AnishNagulavancha/Spoil-Free-Fridge/Data logs/pcb_data/house_A_pcb_A_S0001_Anish_control_empty_20260720_190316/images/img_000002_20260720_193534.jpg

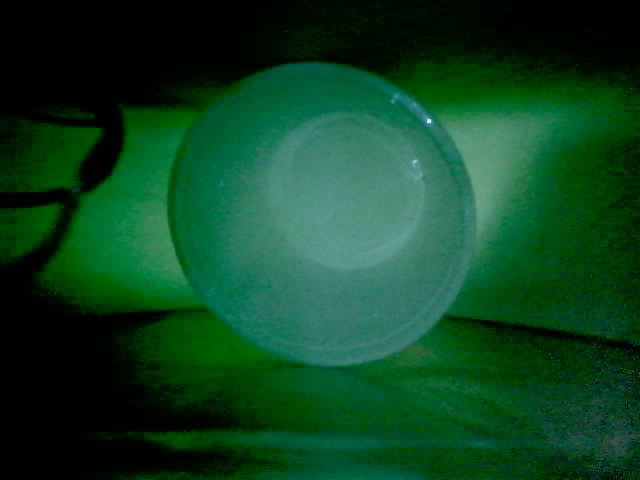
Data logs/pcb_data/house_A_pcb_A_S0001_Anish_control_empty_20260720_190316/images/img_000002_20260720_193534.jpg
