AnishNagulavancha/Spoil-Free-Fridge/Data logs/pcb_data/house_A_pcb_A_S01_Anish_powertest1_control_empty_20260809_191333/images/img_000014_20260809_204405.jpg

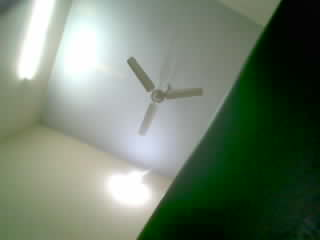
Data logs/pcb_data/house_A_pcb_A_S01_Anish_powertest1_control_empty_20260809_191333/images/img_000014_20260809_204405.jpg
