AnishNagulavancha/Spoil-Free-Fridge/Data logs/pcb_data/house_A_pcb_A_S0001_control_empty_20260720_185718/images/img_000001_20260720_185748.jpg

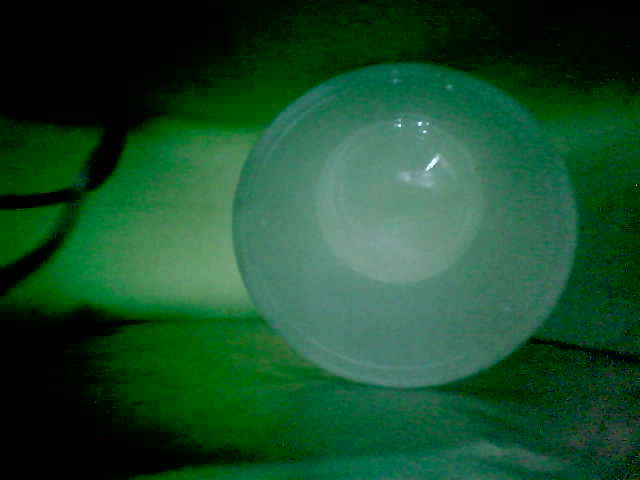
Data logs/pcb_data/house_A_pcb_A_S0001_control_empty_20260720_185718/images/img_000001_20260720_185748.jpg
