AnishNagulavancha/Spoil-Free-Fridge/Data logs/pcb_data/house_A_pcb_A_S0002_Anish_control_empty_20260721_132458/images/img_000044_20260721_173348.jpg

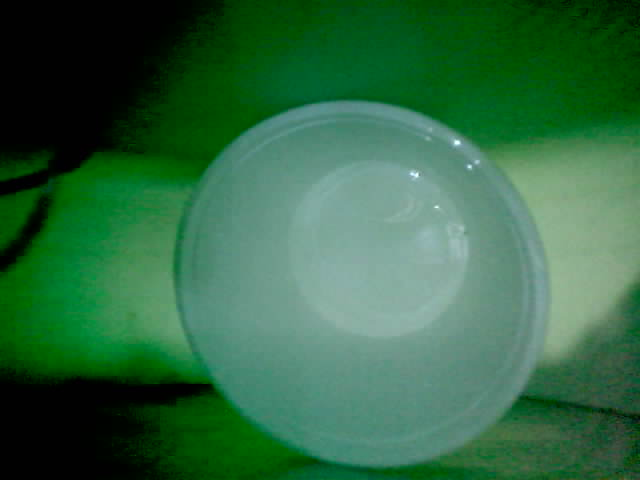
Data logs/pcb_data/house_A_pcb_A_S0002_Anish_control_empty_20260721_132458/images/img_000044_20260721_173348.jpg
