AnishNagulavancha/Spoil-Free-Fridge/Data logs/pcb_data/house_A_pcb_A_S0003_Anish_control_empty_20260721_182247/images/img_000015_20260721_200613.jpg

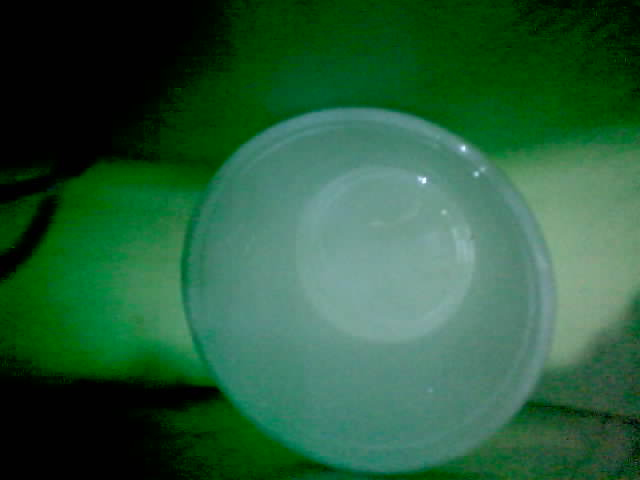
Data logs/pcb_data/house_A_pcb_A_S0003_Anish_control_empty_20260721_182247/images/img_000015_20260721_200613.jpg
