AnishNagulavancha/Spoil-Free-Fridge/Data logs/pcb_data/house_A_pcb_A_S005_Anish_control_empty_20260724_125849/images/img_000001_20260724_125919.jpg

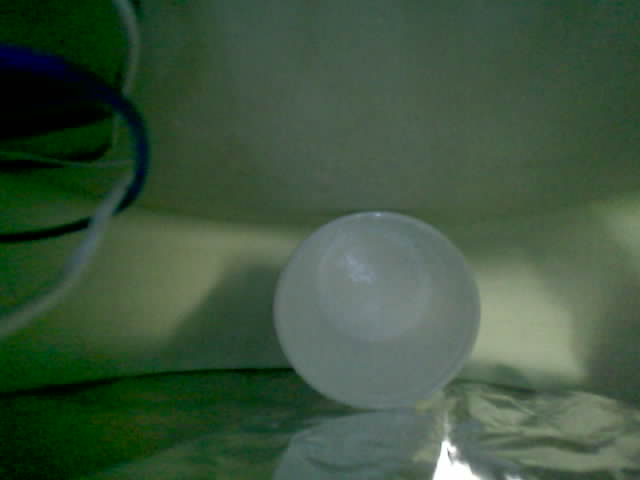
Data logs/pcb_data/house_A_pcb_A_S005_Anish_control_empty_20260724_125849/images/img_000001_20260724_125919.jpg
