AnishNagulavancha/Spoil-Free-Fridge/Data logs/pcb_data/house_A_pcb_A_S005_Anish_control_empty_20260724_125849/images/img_000009_20260724_142733.jpg

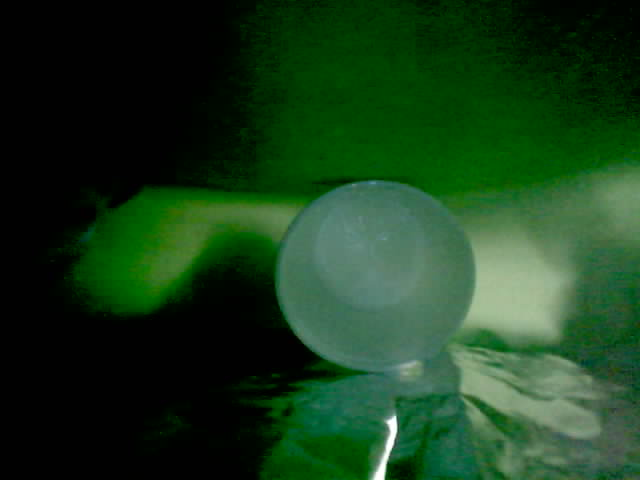
Data logs/pcb_data/house_A_pcb_A_S005_Anish_control_empty_20260724_125849/images/img_000009_20260724_142733.jpg
