AnishNagulavancha/Spoil-Free-Fridge/Data logs/pcb_data/house_A_pcb_A_S006_Anish_control_empty_20260724_222032/images/img_000001_20260724_222102.jpg

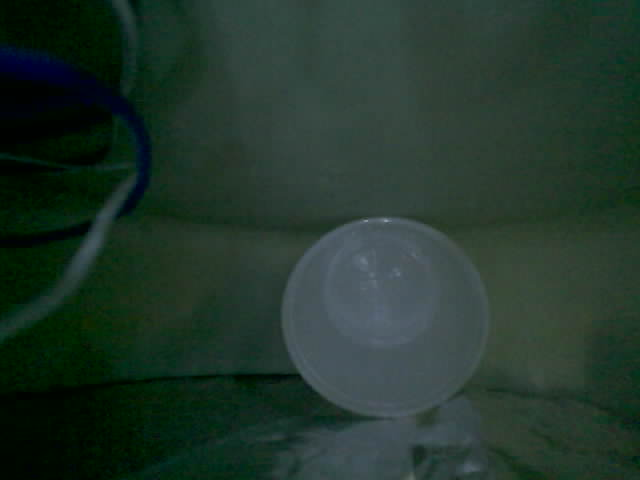
Data logs/pcb_data/house_A_pcb_A_S006_Anish_control_empty_20260724_222032/images/img_000001_20260724_222102.jpg
