AnishNagulavancha/Spoil-Free-Fridge/Data logs/pcb_data/house_A_pcb_A_S006_Anish_control_empty_20260724_222032/images/img_000004_20260724_231115.jpg

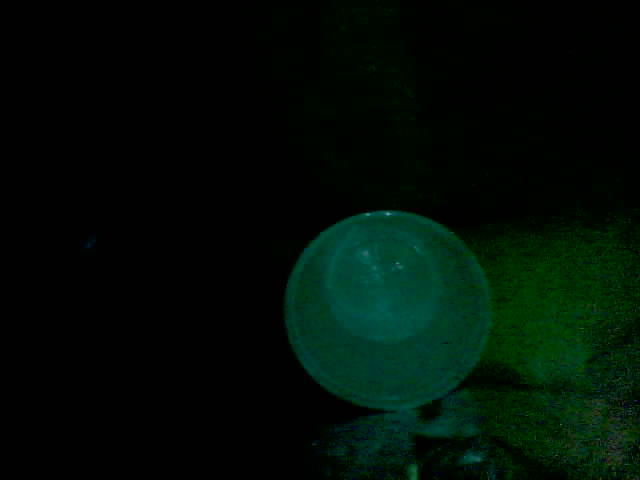
Data logs/pcb_data/house_A_pcb_A_S006_Anish_control_empty_20260724_222032/images/img_000004_20260724_231115.jpg
