AnishNagulavancha/Spoil-Free-Fridge/Data logs/pcb_data/house_A_pcb_A_S007_Anish_control_empty_20260727_212706/images/img_000005_20260727_221510.jpg

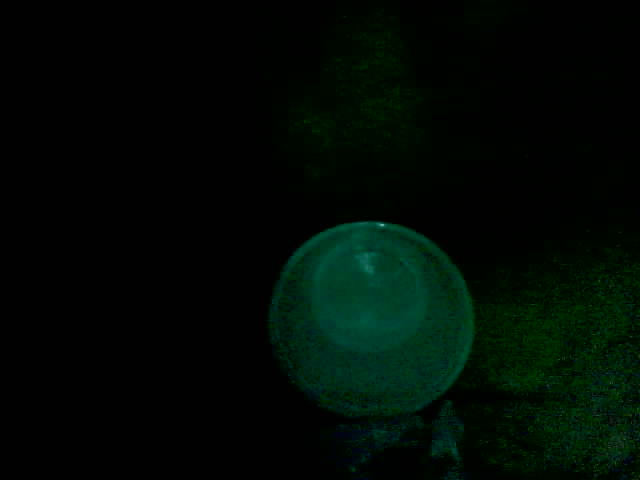
Data logs/pcb_data/house_A_pcb_A_S007_Anish_control_empty_20260727_212706/images/img_000005_20260727_221510.jpg
