AnishNagulavancha/Spoil-Free-Fridge/Data logs/pcb_data/house_A_pcb_A_S007_Anish_control_empty_20260727_212706/images/img_000062_20260728_030009.jpg

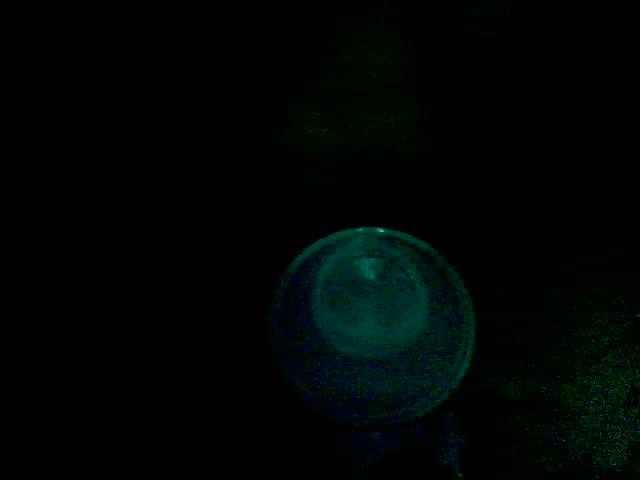
Data logs/pcb_data/house_A_pcb_A_S007_Anish_control_empty_20260727_212706/images/img_000062_20260728_030009.jpg
