AnishNagulavancha/Spoil-Free-Fridge/Data logs/pcb_data/house_A_pcb_A_S011_Anish_pilot_chicken_20260729_115219/images/img_000001_20260729_115249.jpg

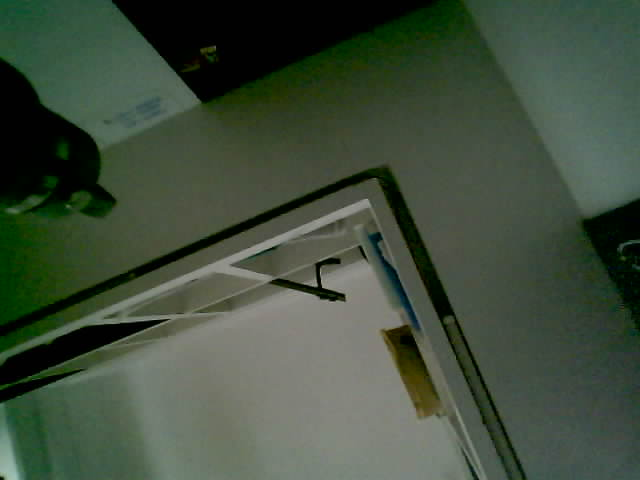
Data logs/pcb_data/house_A_pcb_A_S011_Anish_pilot_chicken_20260729_115219/images/img_000001_20260729_115249.jpg
