AnishNagulavancha/Spoil-Free-Fridge/Data logs/pcb_data/house_A_pcb_A_S012_Anish_chicken2_pilot_chicken_20260802_112823/images/img_000016_20260802_131111.jpg

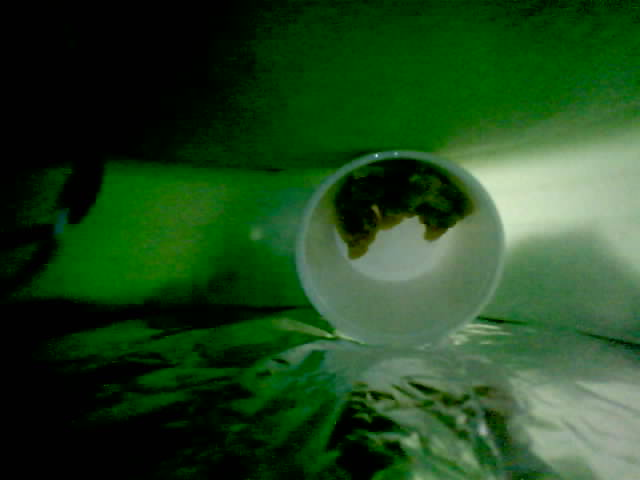
Data logs/pcb_data/house_A_pcb_A_S012_Anish_chicken2_pilot_chicken_20260802_112823/images/img_000016_20260802_131111.jpg
