AnishNagulavancha/Spoil-Free-Fridge/Data logs/pcb_data/house_A_pcb_A_S012_Anish_chicken4_confirmation_chicken_20260805_225737/images/img_000003_20260805_233638.jpg

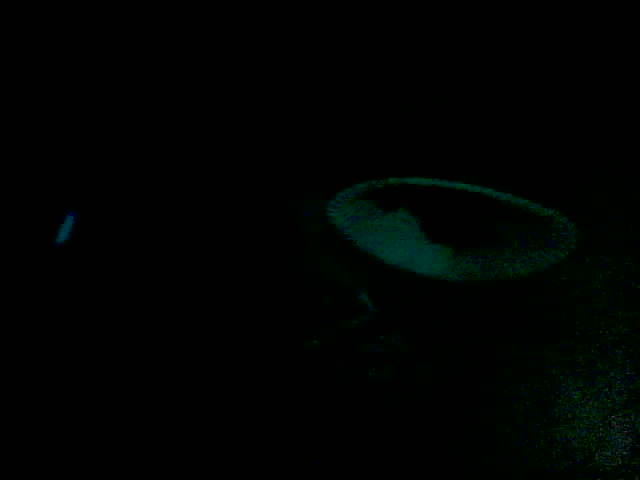
Data logs/pcb_data/house_A_pcb_A_S012_Anish_chicken4_confirmation_chicken_20260805_225737/images/img_000003_20260805_233638.jpg
