AnishNagulavancha/Spoil-Free-Fridge/Data logs/pcb_data/house_A_pcb_A_S012_Anish_powertesttest_control_empty_20260809_185423/images/img_000001_20260809_185453.jpg

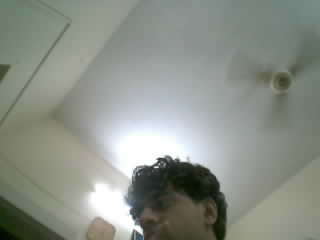
Data logs/pcb_data/house_A_pcb_A_S012_Anish_powertesttest_control_empty_20260809_185423/images/img_000001_20260809_185453.jpg
