AnishNagulavancha/Spoil-Free-Fridge/Data logs/pcb_data/S0001_unknown_20260629_164944/images/img_000002_20260629_165044.jpg

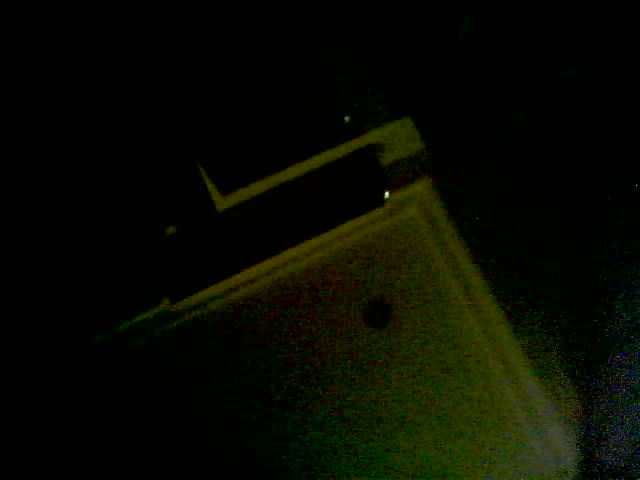
Data logs/pcb_data/S0001_unknown_20260629_164944/images/img_000002_20260629_165044.jpg
