AnishNagulavancha/Spoil-Free-Fridge/Data logs/pcb_data/S0001_unknown_20260629_164944/images/img_000003_20260629_165114.jpg

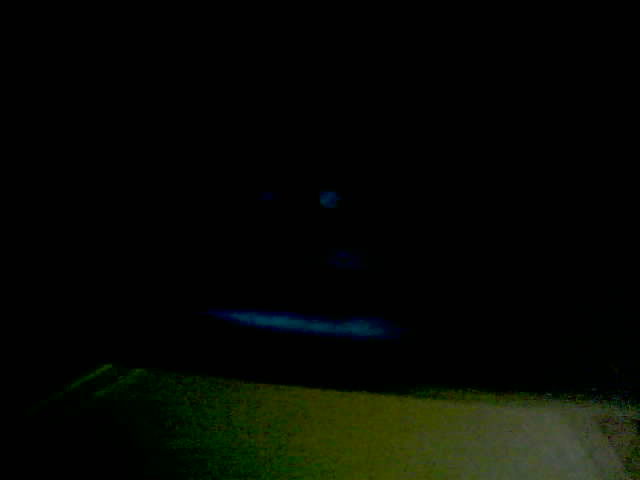
Data logs/pcb_data/S0001_unknown_20260629_164944/images/img_000003_20260629_165114.jpg
