AnishNagulavancha/Spoil-Free-Fridge/Data logs/pcb_data/S0001_unknown_20260711_155523/images/img_000013_20260711_160153.jpg

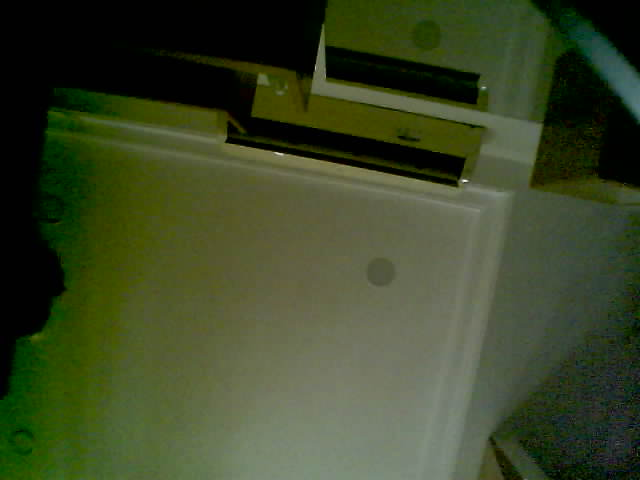
Data logs/pcb_data/S0001_unknown_20260711_155523/images/img_000013_20260711_160153.jpg
