AnishNagulavancha/Spoil-Free-Fridge/Data logs/pcb_data/S0001_unknown_20260711_155523/images/img_000019_20260711_160453.jpg

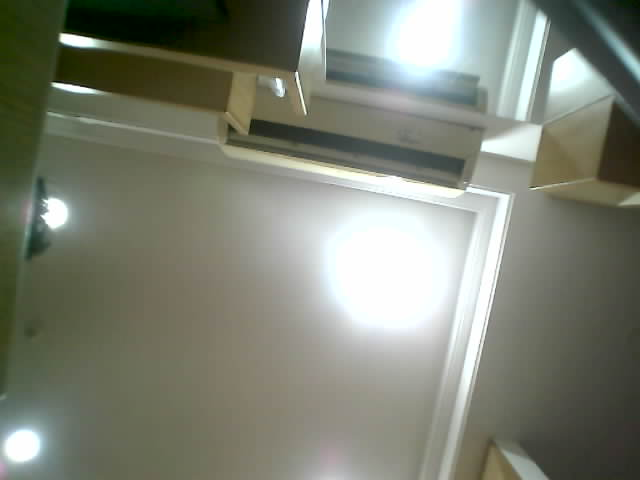
Data logs/pcb_data/S0001_unknown_20260711_155523/images/img_000019_20260711_160453.jpg
