AnishNagulavancha/Spoil-Free-Fridge/firmware/main/wifi_logs/20260810_133253/images/img_000002_20260810_135044.jpg

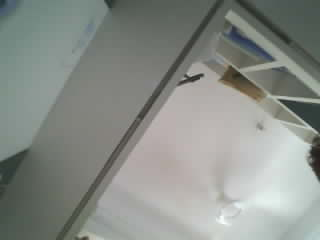
firmware/main/wifi_logs/20260810_133253/images/img_000002_20260810_135044.jpg
