AnishNagulavancha/Spoil-Free-Fridge/firmware/main/wifi_logs/20260810_133253/images/img_000004_20260810_142046.jpg

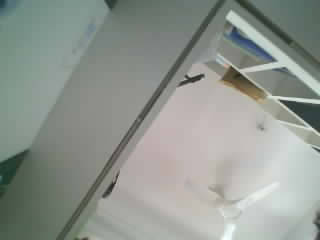
firmware/main/wifi_logs/20260810_133253/images/img_000004_20260810_142046.jpg
