AnishNagulavancha/Spoil-Free-Fridge/firmware/main/wifi_logs/20260810_144159/images/img_000002_20260810_150006.jpg

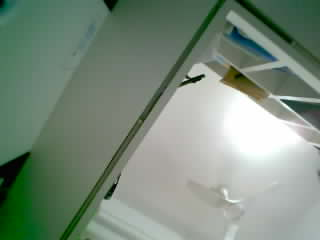
firmware/main/wifi_logs/20260810_144159/images/img_000002_20260810_150006.jpg
