AnishNagulavancha/Spoil-Free-Fridge/firmware/main/main/wifi.c

/* WiFi station Example

   This example code is in the Public Domain (or CC0 licensed, at your option.)

   Unless required by applicable law or agreed to in writing, this
   software is distributed on an "AS IS" BASIS, WITHOUT WARRANTIES OR
   CONDITIONS OF ANY KIND, either express or implied.
*/
#include <string.h>
#include <stdbool.h>
#include "freertos/FreeRTOS.h"
#include "freertos/task.h"
#include "freertos/event_groups.h"
#include "esp_system.h"
#include "esp_wifi.h"
#include "esp_event.h"
#include "esp_log.h"
#include "nvs_flash.h"
#include "wifi.h"

#include "lwip/err.h"
#include "lwip/sys.h"

/* The examples use WiFi configuration that you can set via project configuration menu

   If you'd rather not, just change the below entries to strings with
   the config you want - ie #define EXAMPLE_WIFI_SSID "mywifissid"
*/
#define EXAMPLE_ESP_WIFI_SSID      CONFIG_ESP_WIFI_SSID
#define EXAMPLE_ESP_WIFI_PASS      CONFIG_ESP_WIFI_PASSWORD
#define EXAMPLE_ESP_MAXIMUM_RETRY  CONFIG_ESP_MAXIMUM_RETRY

/* FreeRTOS event group to signal when we are connected*/
static EventGroupHandle_t s_wifi_event_group;

/* The event group allows multiple bits for each event, but we only care about two events:
 * - we are connected to the AP with an IP
 * - we failed to connect after the maximum amount of retries */
#define WIFI_CONNECTED_BIT BIT0
#define WIFI_FAIL_BIT      BIT1

static esp_err_t wifi_init_sta(void);

static const char *TAG = "wifi station";

static int s_retry_num = 0;
static bool s_wifi_stopping;

esp_err_t wifi_init(void) {
    esp_err_t ret = nvs_flash_init();
    if (ret == ESP_ERR_NVS_NO_FREE_PAGES || ret == ESP_ERR_NVS_NEW_VERSION_FOUND) {
      ESP_ERROR_CHECK(nvs_flash_erase());
      ret = nvs_flash_init();
    }
    ESP_ERROR_CHECK(ret);

        if (CONFIG_LOG_MAXIMUM_LEVEL > CONFIG_LOG_DEFAULT_LEVEL) {
        /* If you only want to open more logs in the wifi module, you need to make the max level greater than the default level,
         * and call esp_log_level_set() before esp_wifi_init() to improve the log level of the wifi module. */
        esp_log_level_set("wifi", CONFIG_LOG_MAXIMUM_LEVEL);
    }

    ESP_LOGI(TAG, "ESP_WIFI_MODE_STA");
    return wifi_init_sta();

}

esp_err_t wifi_start(void)
{
    if (s_wifi_event_group == NULL) {
        return ESP_ERR_INVALID_STATE;
    }

    s_retry_num = 0;
    s_wifi_stopping = false;
    xEventGroupClearBits(s_wifi_event_group,
                         WIFI_CONNECTED_BIT | WIFI_FAIL_BIT);

    esp_err_t result = esp_wifi_start();
    if (result != ESP_OK) {
        ESP_LOGE(TAG, "Failed to start Wi-Fi: %s", esp_err_to_name(result));
        return result;
    }

    EventBits_t bits = xEventGroupWaitBits(
        s_wifi_event_group,
        WIFI_CONNECTED_BIT | WIFI_FAIL_BIT,
        pdFALSE,
        pdFALSE,
        portMAX_DELAY);

    if (bits & WIFI_CONNECTED_BIT) {
        ESP_LOGI(TAG, "Wi-Fi restarted and received an IP address");
        return ESP_OK;
    }

    ESP_LOGE(TAG, "Wi-Fi restart failed after maximum retries");
    return ESP_FAIL;
}

esp_err_t wifi_stop(void)
{
    s_wifi_stopping = true;
    esp_err_t result = esp_wifi_stop();
    if (result != ESP_OK) {
        s_wifi_stopping = false;
        ESP_LOGE(TAG, "Failed to stop Wi-Fi: %s", esp_err_to_name(result));
        return result;
    }

    ESP_LOGI(TAG, "Wi-Fi stopped successfully");
    return ESP_OK;
}


static void event_handler(void* arg, esp_event_base_t event_base,
                                int32_t event_id, void* event_data)
{
    if (event_base == WIFI_EVENT && event_id == WIFI_EVENT_STA_START) {
        esp_wifi_connect();
    } else if (event_base == WIFI_EVENT && event_id == WIFI_EVENT_STA_DISCONNECTED) {
        if (s_wifi_stopping) {
            return;
        }
        if (s_retry_num < EXAMPLE_ESP_MAXIMUM_RETRY) {
            esp_wifi_connect();
            s_retry_num++;
            ESP_LOGI(TAG, "retry to connect to the AP");
        } else {
            xEventGroupSetBits(s_wifi_event_group, WIFI_FAIL_BIT);
        }
        ESP_LOGI(TAG,"connect to the AP fail");
    } else if (event_base == IP_EVENT && event_id == IP_EVENT_STA_GOT_IP) {
        ip_event_got_ip_t* event = (ip_event_got_ip_t*) event_data;
        ESP_LOGI(TAG, "got ip:" IPSTR, IP2STR(&event->ip_info.ip));
        s_retry_num = 0;
        xEventGroupSetBits(s_wifi_event_group, WIFI_CONNECTED_BIT);
    }
}

static esp_err_t wifi_init_sta(void)
{
    s_wifi_event_group = xEventGroupCreate();

    ESP_ERROR_CHECK(esp_netif_init());

    ESP_ERROR_CHECK(esp_event_loop_create_default());
    esp_netif_create_default_wifi_sta();

    wifi_init_config_t cfg = WIFI_INIT_CONFIG_DEFAULT();
    ESP_ERROR_CHECK(esp_wifi_init(&cfg));

    esp_event_handler_instance_t instance_any_id;
    esp_event_handler_instance_t instance_got_ip;
    ESP_ERROR_CHECK(esp_event_handler_instance_register(WIFI_EVENT,
                                                        ESP_EVENT_ANY_ID,
                                                        &event_handler,
                                                        NULL,
                                                        &instance_any_id));
    ESP_ERROR_CHECK(esp_event_handler_instance_register(IP_EVENT,
                                                        IP_EVENT_STA_GOT_IP,
                                                        &event_handler,
                                                        NULL,
                                                        &instance_got_ip));

    wifi_config_t wifi_config = {
        .sta = {
            .ssid = EXAMPLE_ESP_WIFI_SSID,
            .password = EXAMPLE_ESP_WIFI_PASS,
            /* Authmode threshold resets to WPA2 as default if password matches WPA2 standards (password len => 8).
             * If you want to connect the device to deprecated WEP/WPA networks, Please set the threshold value
             * to WIFI_AUTH_WEP/WIFI_AUTH_WPA_PSK and set the password with length and format matching to
             * WIFI_AUTH_WEP/WIFI_AUTH_WPA_PSK standards.
             */
            // .threshold.authmode = ESP_WIFI_SCAN_AUTH_MODE_THRESHOLD,
            // .sae_pwe_h2e = ESP_WIFI_SAE_MODE,
            // .sae_h2e_identifier = EXAMPLE_H2E_IDENTIFIER,
#ifdef CONFIG_ESP_WIFI_WPA3_COMPATIBLE_SUPPORT
            .disable_wpa3_compatible_mode = 0,
#endif
        },
    };
    ESP_ERROR_CHECK(esp_wifi_set_mode(WIFI_MODE_STA) );
    ESP_ERROR_CHECK(esp_wifi_set_config(WIFI_IF_STA, &wifi_config) );
    ESP_ERROR_CHECK(esp_wifi_start() );

    ESP_LOGI(TAG, "wifi_init_sta finished.");

    /* Waiting until either the connection is established (WIFI_CONNECTED_BIT) or connection failed for the maximum
     * number of re-tries (WIFI_FAIL_BIT). The bits are set by event_handler() (see above) */
    EventBits_t bits = xEventGroupWaitBits(s_wifi_event_group,
            WIFI_CONNECTED_BIT | WIFI_FAIL_BIT,
            pdFALSE,
            pdFALSE,
            portMAX_DELAY);

    /* xEventGroupWaitBits() returns the bits before the call returned, hence we can test which event actually
     * happened. */
    if (bits & WIFI_CONNECTED_BIT) {
        ESP_LOGI(TAG, "connected to ap SSID:%s",
                 EXAMPLE_ESP_WIFI_SSID);
        return ESP_OK;
    } else if (bits & WIFI_FAIL_BIT) {
        ESP_LOGE(TAG, "Failed to connect to SSID:%s",
                 EXAMPLE_ESP_WIFI_SSID);
        return ESP_FAIL;
    } else {
        ESP_LOGE(TAG, "UNEXPECTED EVENT");
        return ESP_FAIL;
    }
}
