AnishNagulavancha/Spoil-Free-Fridge/firmware/main/main/camera.h

#pragma once

#include "esp_err.h"

#ifdef BOARD_ESP32S3_XIAO
#define CAM_PIN_PWDN -1
#define CAM_PIN_RESET -1   //software reset will be performed
#define CAM_PIN_VSYNC 38
#define CAM_PIN_HREF 47
#define CAM_PIN_PCLK 13
#define CAM_PIN_XCLK 10
#define CAM_PIN_SIOD 40
#define CAM_PIN_SIOC 39
#define CAM_PIN_D0 15
#define CAM_PIN_D1 17
#define CAM_PIN_D2 18
#define CAM_PIN_D3 16
#define CAM_PIN_D4 14
#define CAM_PIN_D5 12
#define CAM_PIN_D6 11
#define CAM_PIN_D7 48
#endif

esp_err_t init_camera(void);
esp_err_t deinit_camera(void);
