AnishNagulavancha/Spoil-Free-Fridge/firmware/main/main/i2c_bus.h

#pragma once

#include "esp_err.h"
#include "driver/i2c_master.h"

#define I2C_MASTER_PORT I2C_NUM_0
#define I2C_MASTER_SDA_IO GPIO_NUM_5
#define I2C_MASTER_SCL_IO GPIO_NUM_6

esp_err_t i2c_master_init(void);
i2c_master_bus_handle_t i2c_bus_get_handle(void);
